c-/ESP32-Ethgate/ESP32-Ethgate-firmware/Private.h

#ifndef PRIVATE_H
#define PRIVATE_H

#define WIFI_CHANNEL    7
#define MQTT_SERVER "192.168.1.24"
#define MQTT_USER "esp"
#define MQTT_PASS "especially"
#define OTA_PASSWORD "will work 4 food"

#endif
